croningp/NanoDiscovery/Theory/PyDScat-GPU/Examples/Core_shell/exp6/atomList_TruncatedOctahedron10.png

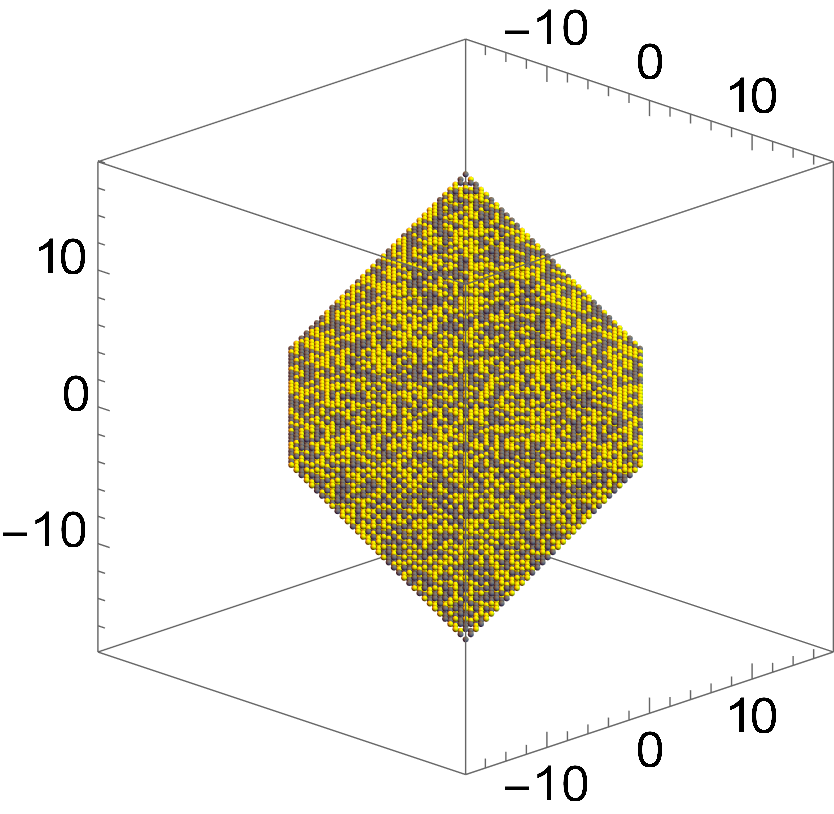
Theory/PyDScat-GPU/Examples/Core_shell/exp6/atomList_TruncatedOctahedron10.png
