croningp/NanoDiscovery/Theory/Superellipsoid/Experiment_20_20_20_1_1/Dipole.png

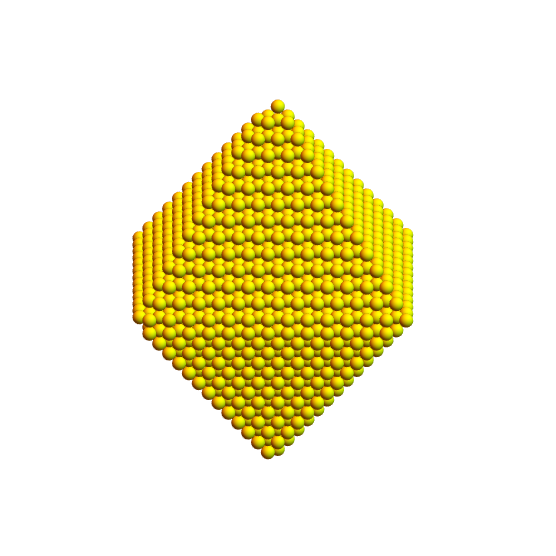
Theory/Superellipsoid/Experiment_20_20_20_1_1/Dipole.png
