croningp/NanoDiscovery/Theory/PyDScat-GPU/Examples/Core_shell/atomList_Octahedron.csv

Ag | 0. | 0. | 34.
Au | 0. | 0.5 | 33.5
Ag | 0. | 1. | 33.
Au | 0. | 1.5 | 32.5
Ag | 0. | 2. | 32.
Au | 0. | 2.5 | 31.5
Ag | 0. | 3. | 31.
Ag | 0. | 3.5 | 30.5
Au | 0. | 4. | 30.
Ag | 0. | 4.5 | 29.5
Au | 0. | 5. | 29.
Ag | 0. | 5.5 | 28.5
Ag | 0. | 6. | 28.
Ag | 0. | 6.5 | 27.5
Ag | 0. | 7. | 27.
Au | 0. | 7.5 | 26.5
Ag | 0. | 8. | 26.
Ag | 0. | 8.5 | 25.5
Ag | 0. | 9. | 25.
Au | 0. | 9.5 | 24.5
Ag | 0. | 10. | 24.
Ag | 0. | 10.5 | 23.5
Au | 0. | 11. | 23.
Ag | 0. | 11.5 | 22.5
Ag | 0. | 12. | 22.
Au | 0. | 12.5 | 21.5
Au | 0. | 13. | 21.
Ag | 0. | 13.5 | 20.5
Au | 0. | 14. | 20.
Au | 0. | 14.5 | 19.5
Ag | 0. | 15. | 19.
Ag | 0. | 15.5 | 18.5
Ag | 0. | 16. | 18.
Ag | 0. | 16.5 | 17.5
Ag | 0. | 17. | 17.
Au | 0. | 17.5 | 16.5
Ag | 0. | 18. | 16.
Ag | 0. | 18.5 | 15.5
Ag | 0. | 19. | 15.
Ag | 0. | 19.5 | 14.5
Au | 0. | 20. | 14.
Ag | 0. | 20.5 | 13.5
Ag | 0. | 21. | 13.
Au | 0. | 21.5 | 12.5
Ag | 0. | 22. | 12.
Ag | 0. | 22.5 | 11.5
Au | 0. | 23. | 11.
Au | 0. | 23.5 | 10.5
Au | 0. | 24. | 10.
Au | 0. | 24.5 | 9.5
Ag | 0. | 25. | 9.
Au | 0. | 25.5 | 8.5
Au | 0. | 26. | 8.
Au | 0. | 26.5 | 7.5
Au | 0. | 27. | 7.
Au | 0. | 27.5 | 6.5
Au | 0. | 28. | 6.
Au | 0. | 28.5 | 5.5
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
