croningp/NanoDiscovery/Theory/PyDScat-GPU/Examples/Heter_samples/exp7_custom/custom_ratio.csv

8.000000000000000444e-01 | 8.000000000000000444e-01 | 8.000000000000000444e-01 | 8.000000000000000444e-01 | 8.000000000000000444e-01 | 8.000000000000000444e-01 | 8.000000000000000444e-01 | 8.000000000000000444e-01 | 8.000000000000000444e-01 | 8.000000000000000444e-01 | 8.000000000000000444e-01 | 8.000000000000000444e-01 | 8.000000000000000444e-01 | 8.000000000000000444e-01 | 8.000000000000000444e-01 | 8.000000000000000444e-01 | 8.000000000000000444e-01 | 8.000000000000000444e-01 | 8.000000000000000444e-01 | 8.000000000000000444e-01 | 8.000000000000000444e-01 | 8.000000000000000444e-01 | 8.000000000000000444e-01 | 8.000000000000000444e-01 | 8.000000000000000444e-01 | 8.000000000000000444e-01 | 8.000000000000000444e-01 | 8.000000000000000444e-01 | 8.000000000000000444e-01 | 8.000000000000000444e-01 | 8.000000000000000444e-01 | 8.000000000000000444e-01 | 8.000000000000000444e-01 | 8.000000000000000444e-01 | 8.000000000000000444e-01 | 8.000000000000000444e-01 | 8.000000000000000444e-01 | 8.000000000000000444e-01 | 8.000000000000000444e-01 | 8.000000000000000444e-01 | 8.000000000000000444e-01 | 8.000000000000000444e-01 | 8.000000000000000444e-01 | 8.000000000000000444e-01 |
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
