croningp/NanoDiscovery/Experiments/Graph_Structure/hardware_graph.png

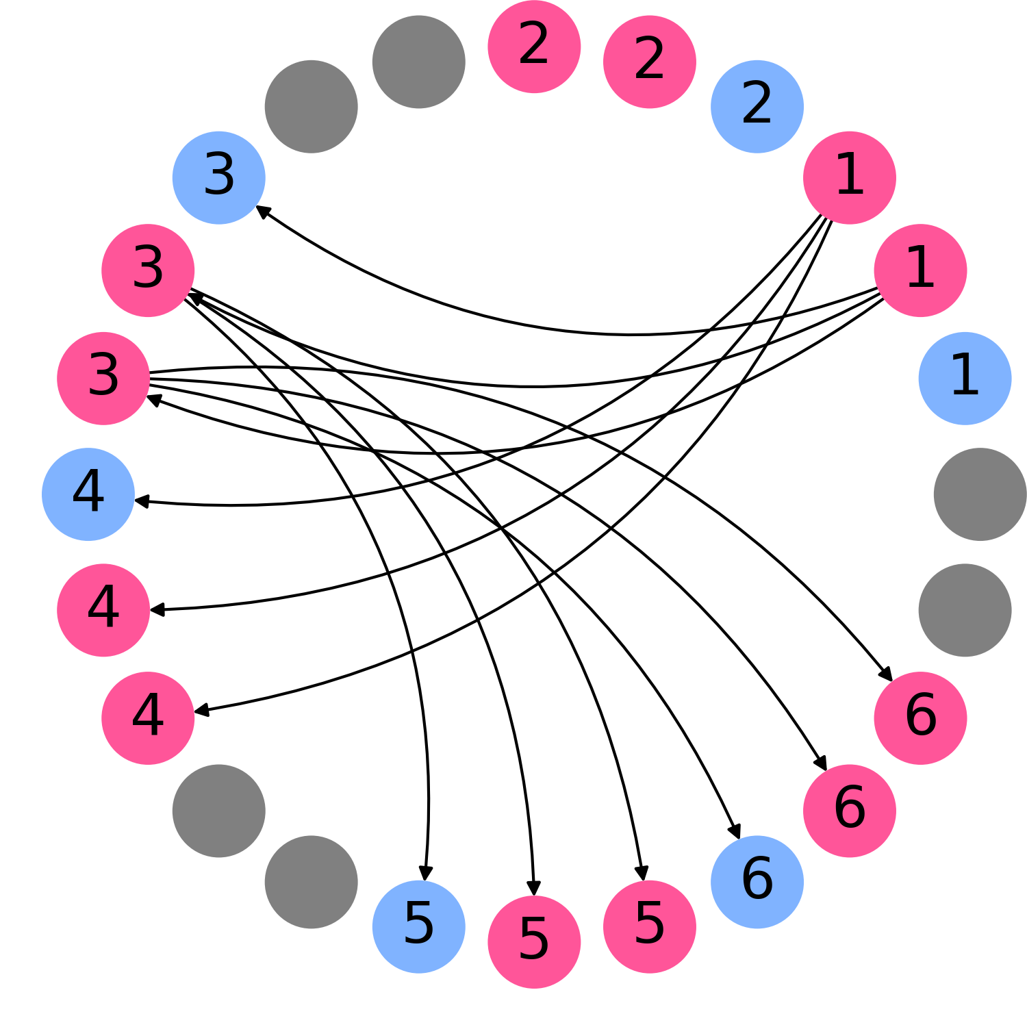
Experiments/Graph_Structure/hardware_graph.png
