croningp/NanoDiscovery/Experiments/Graph_Structure/synthesis_graph.png

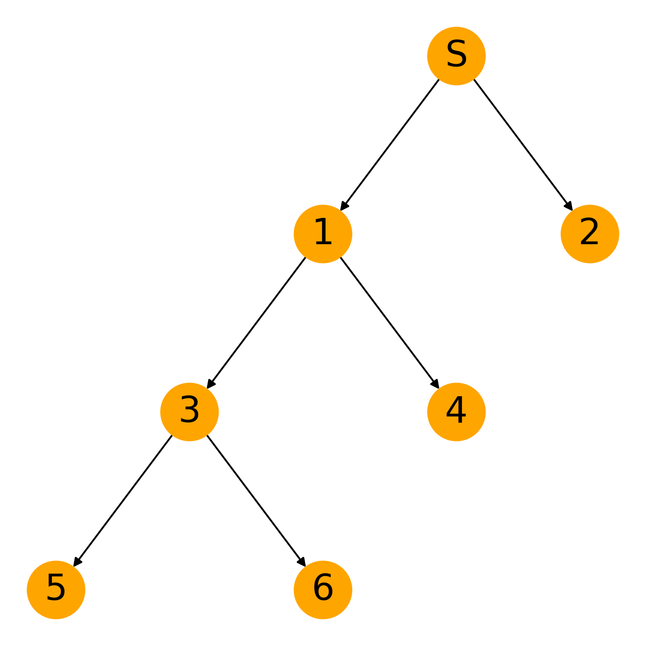
Experiments/Graph_Structure/synthesis_graph.png
