croningp/NanoDiscovery/Theory/PyDScat-GPU/Examples/Au_Ag_coreshell.png

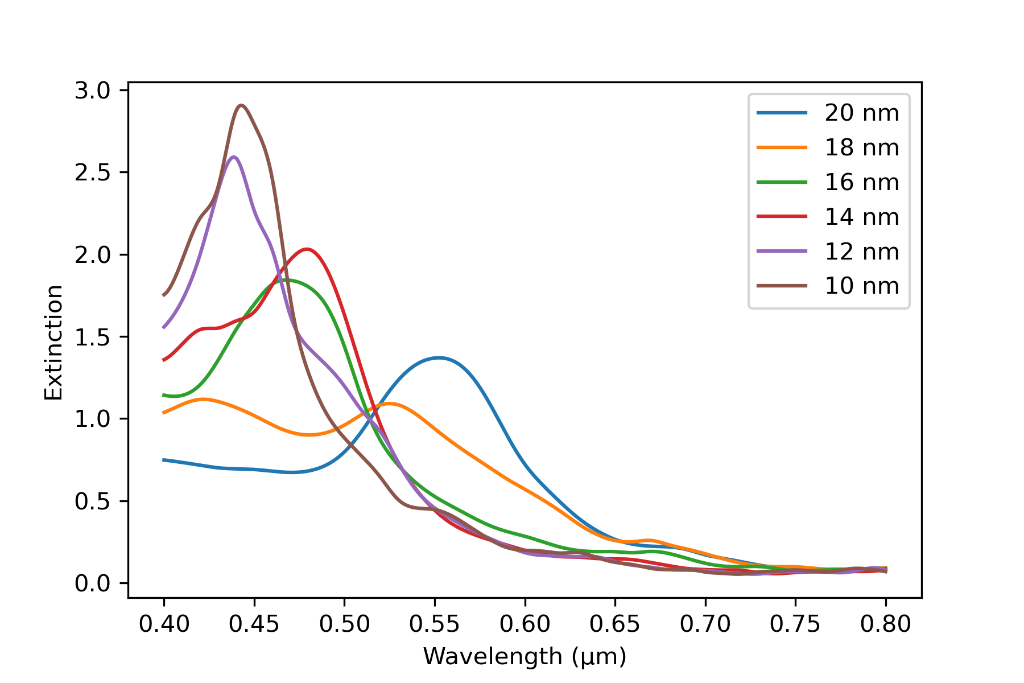
Theory/PyDScat-GPU/Examples/Au_Ag_coreshell.png
