croningp/NanoDiscovery/Theory/PyDScat-GPU/Examples/Au_Ag_homo.png

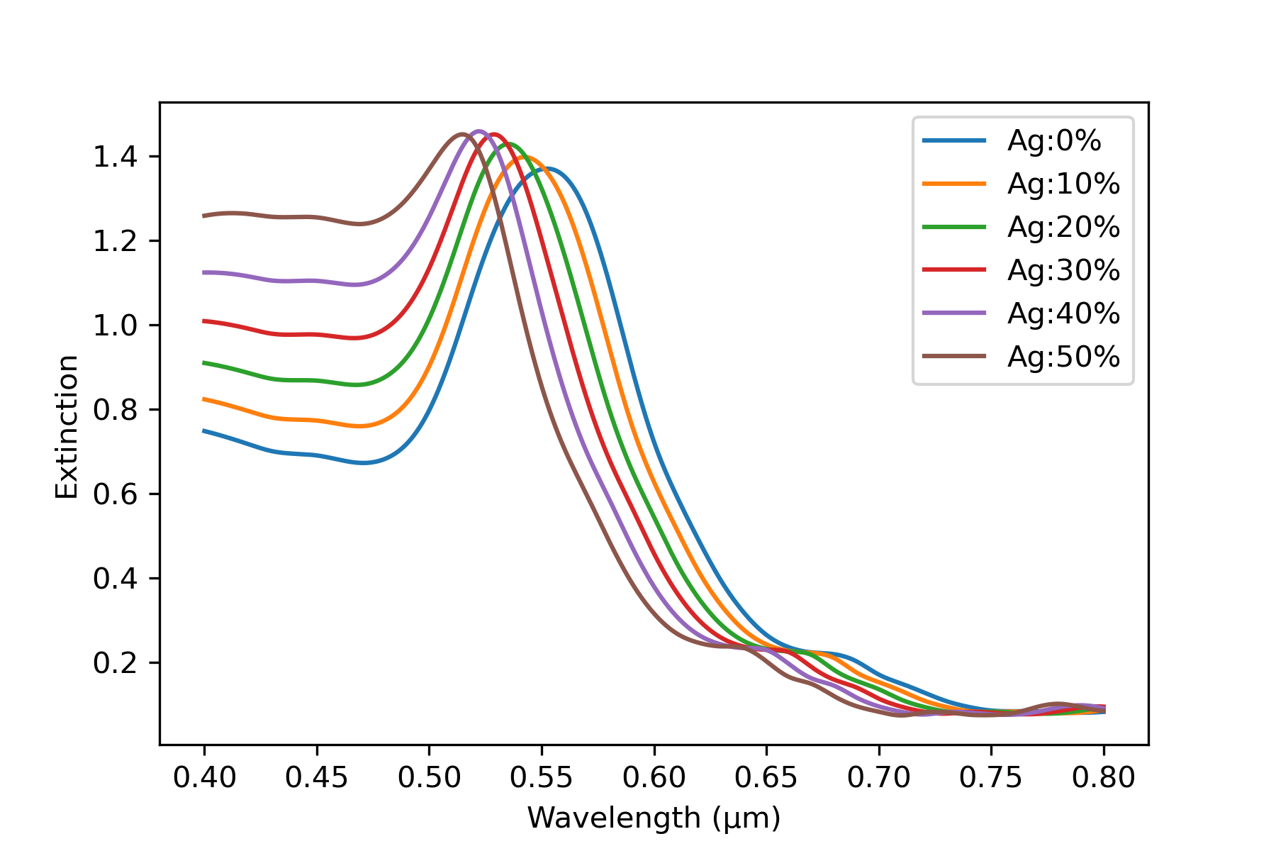
Theory/PyDScat-GPU/Examples/Au_Ag_homo.png
