croningp/NanoDiscovery/Theory/PyDScat-GPU/Examples/Core_shell/exp1/dipolePlot.png

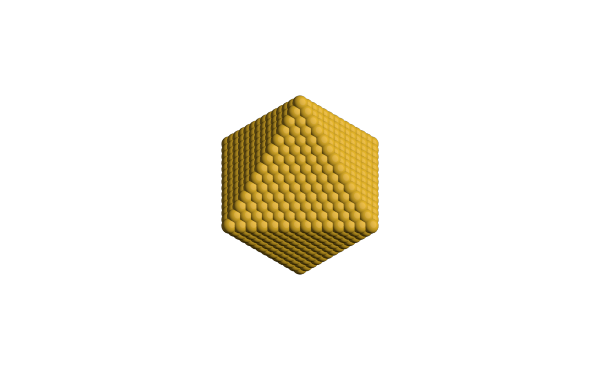
Theory/PyDScat-GPU/Examples/Core_shell/exp1/dipolePlot.png
