croningp/NanoDiscovery/Theory/PyDScat-GPU/Examples/Core_shell/exp5/atomList_TruncatedOctahedron12.png

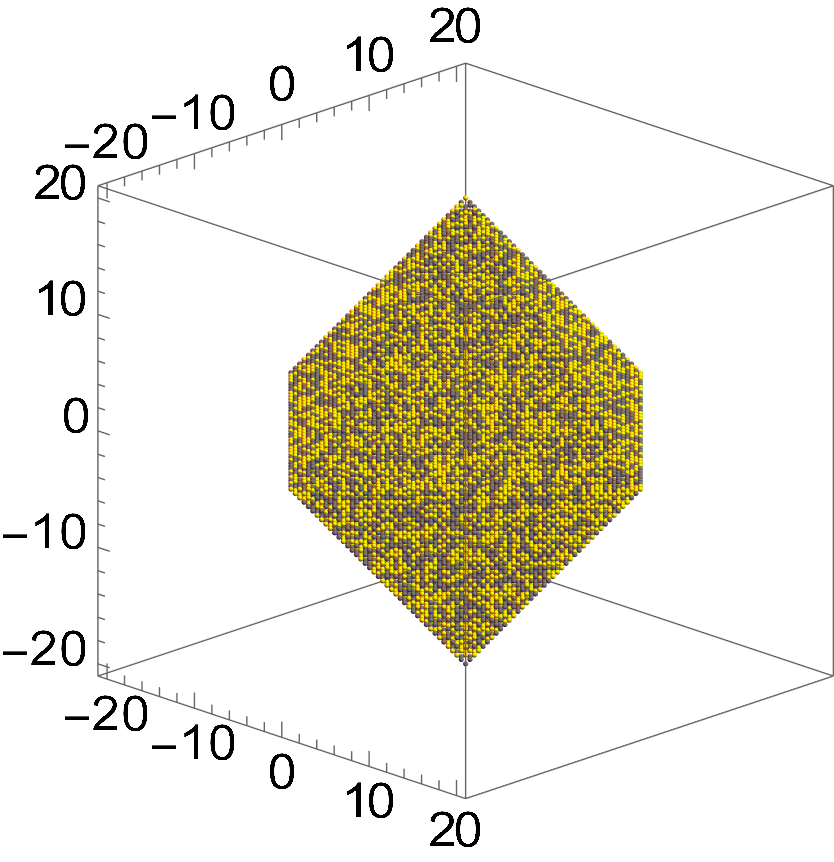
Theory/PyDScat-GPU/Examples/Core_shell/exp5/atomList_TruncatedOctahedron12.png
