croningp/NanoDiscovery/Theory/PyDScat-GPU/Examples/Core_shell/exp5/UV_Vis.png

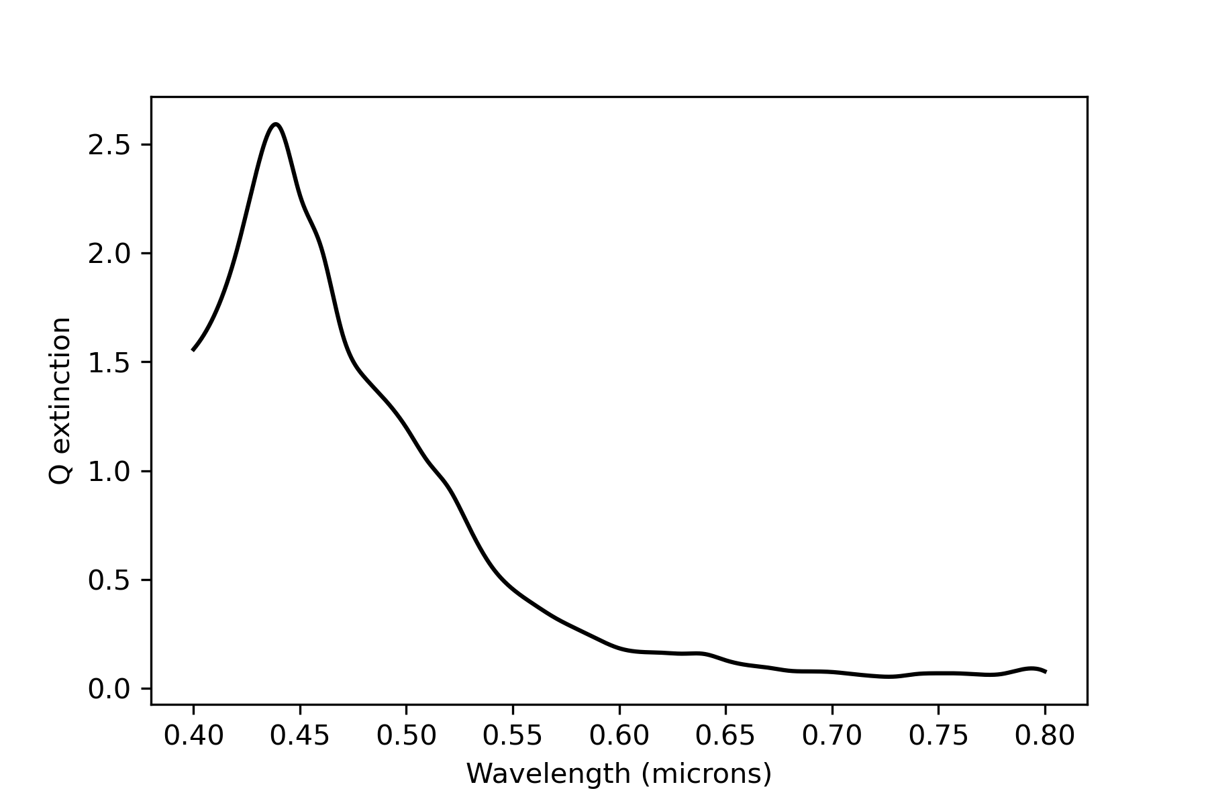
Theory/PyDScat-GPU/Examples/Core_shell/exp5/UV_Vis.png
