croningp/NanoDiscovery/Theory/PyDScat-GPU/Examples/Core_shell/exp6/UV_Vis.png

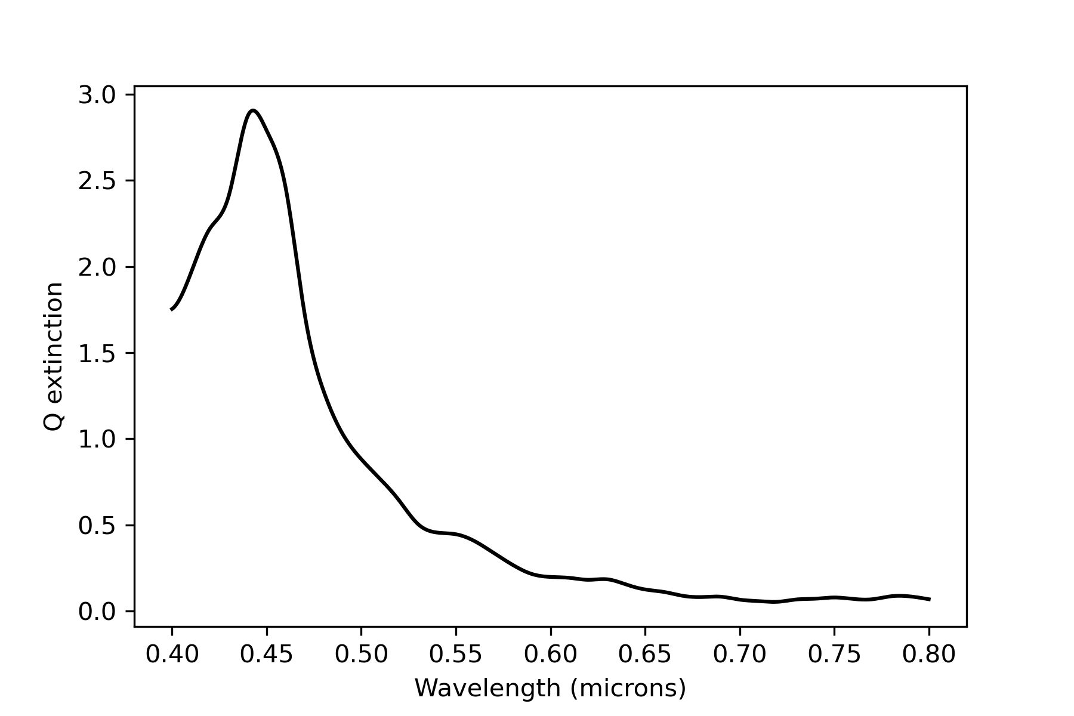
Theory/PyDScat-GPU/Examples/Core_shell/exp6/UV_Vis.png
