croningp/NanoDiscovery/Theory/PyDScat-GPU/Examples/Heter_samples/exp3/UV_Vis.png

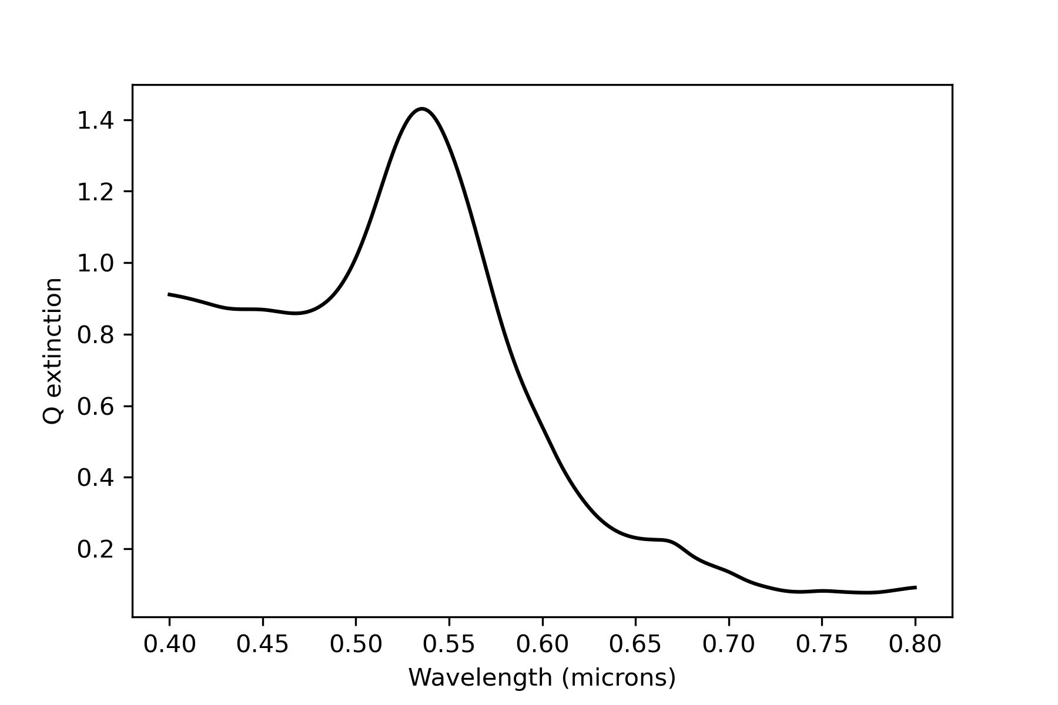
Theory/PyDScat-GPU/Examples/Heter_samples/exp3/UV_Vis.png
