croningp/NanoDiscovery/Theory/PyDScat-GPU/Examples/Heter_samples/exp5/UV_Vis.png

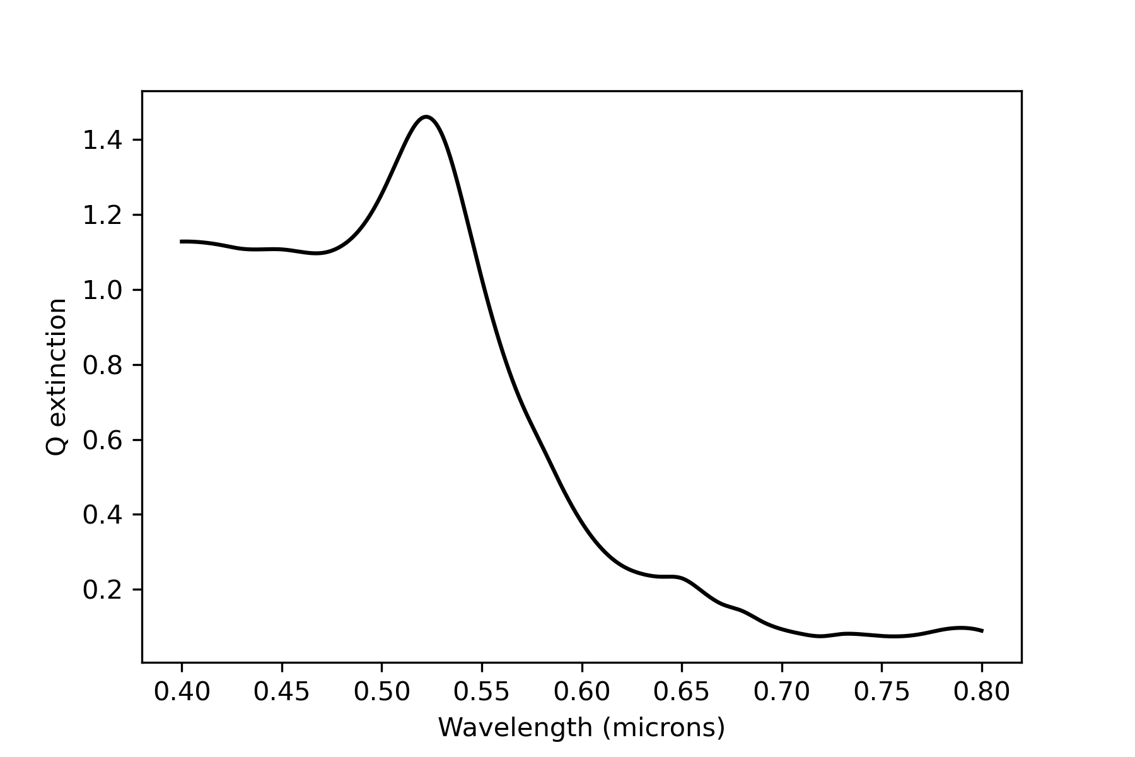
Theory/PyDScat-GPU/Examples/Heter_samples/exp5/UV_Vis.png
