croningp/NanoDiscovery/Experiments/Hardware/Spectroscopic suite/Cuts/Flow cell balcony base plate.dxf

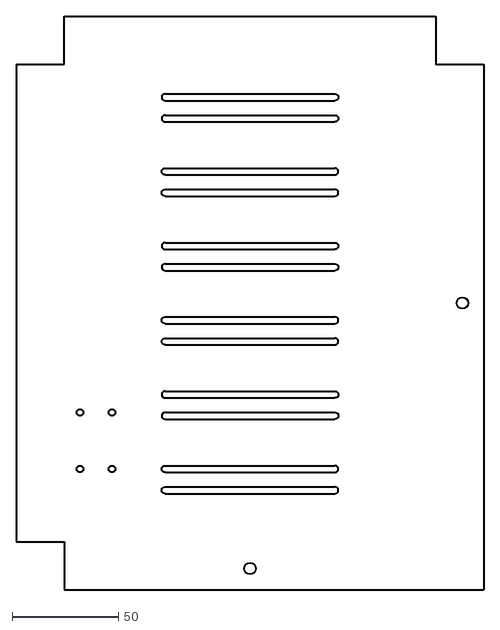
[picture p36: CAD file, 2022-08-24]
Experiments/Hardware/Spectroscopic suite/Cuts/Flow cell balcony base plate.dxf
220.0 x 270.0
