croningp/NanoDiscovery/Experiments/Hardware/Spectroscopic suite/Prints/Spectrometer shelf mount right.stl

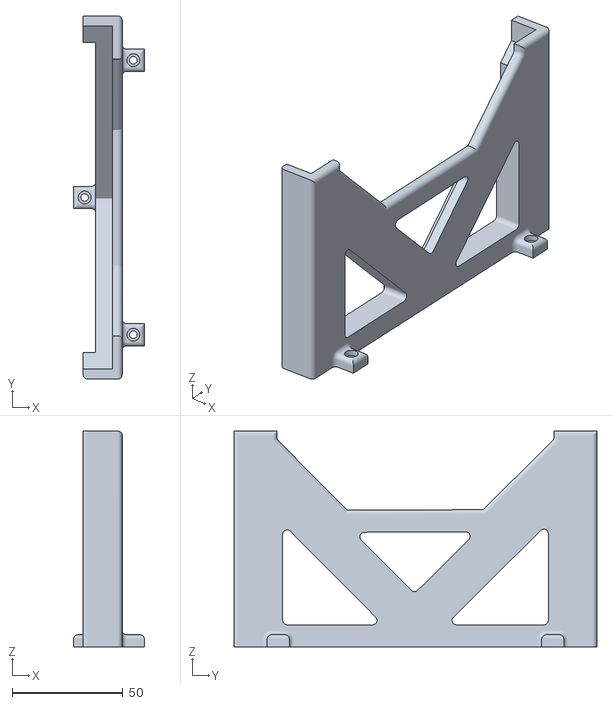
[picture p37: CAD file, 2022-08-24]
Experiments/Hardware/Spectroscopic suite/Prints/Spectrometer shelf mount right.stl
32.0 x 164.0 x 97.5
