croningp/NanoDiscovery/Experiments/Hardware/Tri-Cont shelf/Cuts/Tricont v-slot box - Base for 12 pumps 6mm.dxf

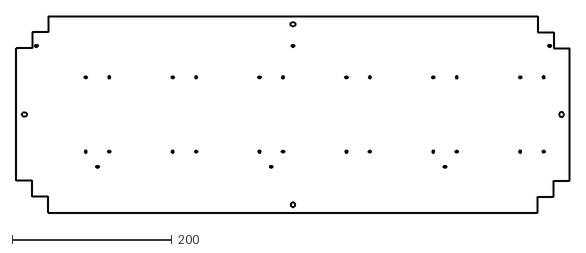
[picture p38: CAD file, 2022-08-24]
Experiments/Hardware/Tri-Cont shelf/Cuts/Tricont v-slot box - Base for 12 pumps 6mm.dxf
692.8 x 246.0
