croningp/NanoDiscovery/Experiments/Hardware/Tri-Cont shelf/Prints/Tri-cont printed stand.stl

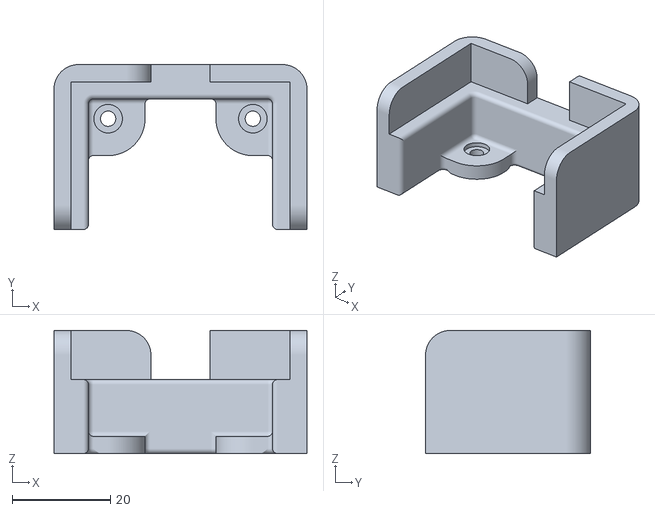
[picture p39: CAD file, 2022-08-24]
Experiments/Hardware/Tri-Cont shelf/Prints/Tri-cont printed stand.stl
51.4 x 33.5 x 25.0
