croningp/NanoDiscovery/Experiments/Software/modularwheelplatform/docs/hardware/Prints/Dispensing unit/Kinesis needles/ClusterBot/Dispensing module Kinesis needles ClusterBot Inlay.stl

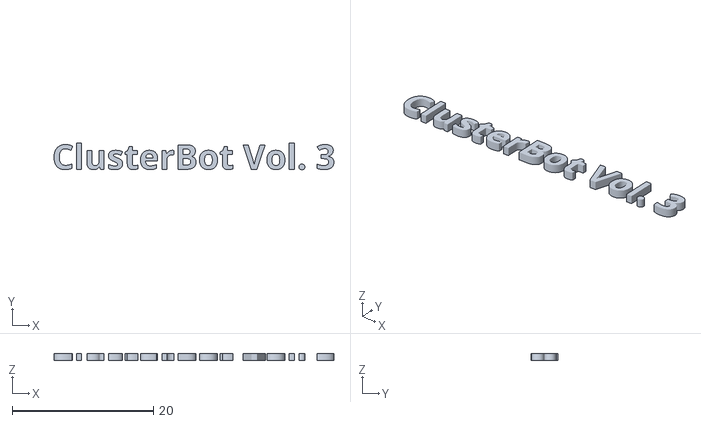
[picture p40: CAD file, 2022-08-24]
Experiments/Software/modularwheelplatform/docs/hardware/Prints/Dispensing unit/Kinesis needles/ClusterBot/Dispensing module Kinesis needles ClusterBot Inlay.stl
39.6 x 3.76 x 1.00
