croningp/NanoDiscovery/Experiments/Software/modularwheelplatform/docs/hardware/Prints/Dispensing unit/Kinesis needles/MapleBot/Dispensing module Kinesis needles MapleBot- inlay.stl

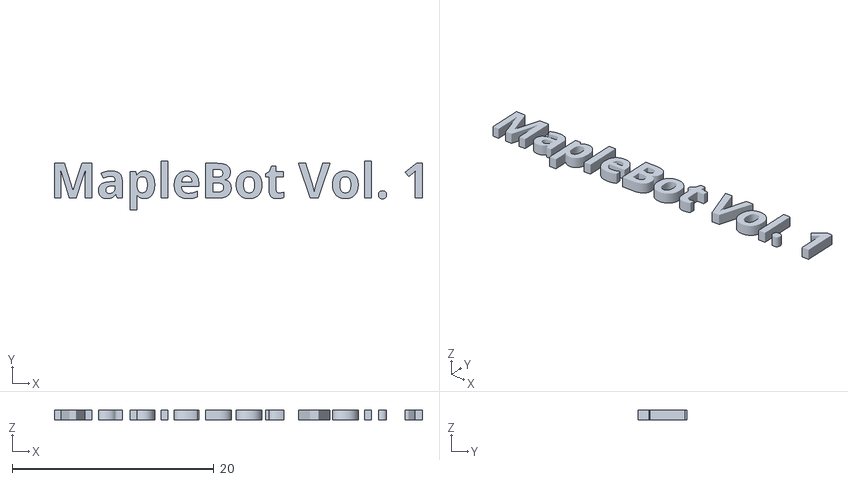
[picture p41: CAD file, 2022-08-24]
Experiments/Software/modularwheelplatform/docs/hardware/Prints/Dispensing unit/Kinesis needles/MapleBot/Dispensing module Kinesis needles MapleBot- inlay.stl
36.5 x 4.86 x 1.00
