croningp/NanoDiscovery/Experiments/Software/modularwheelplatform/docs/hardware/Prints/Dispensing unit/Kinesis needles/Modular wheel/Dispensing module 7 Kinesis needles - MW inlay.stl

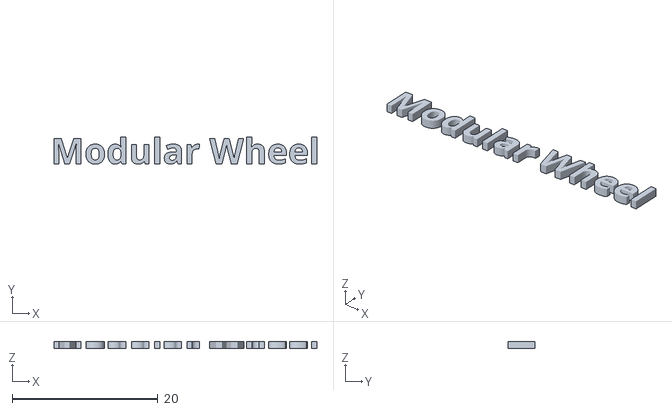
[picture p42: CAD file, 2022-08-24]
Experiments/Software/modularwheelplatform/docs/hardware/Prints/Dispensing unit/Kinesis needles/Modular wheel/Dispensing module 7 Kinesis needles - MW inlay.stl
36.1 x 3.74 x 1.00
