croningp/NanoDiscovery/Experiments/Software/modularwheelplatform/docs/hardware/Prints/Dispensing unit/Kinesis needles/NanoBot/Dispensing module Kinesis needles NanoBot Inlay.stl

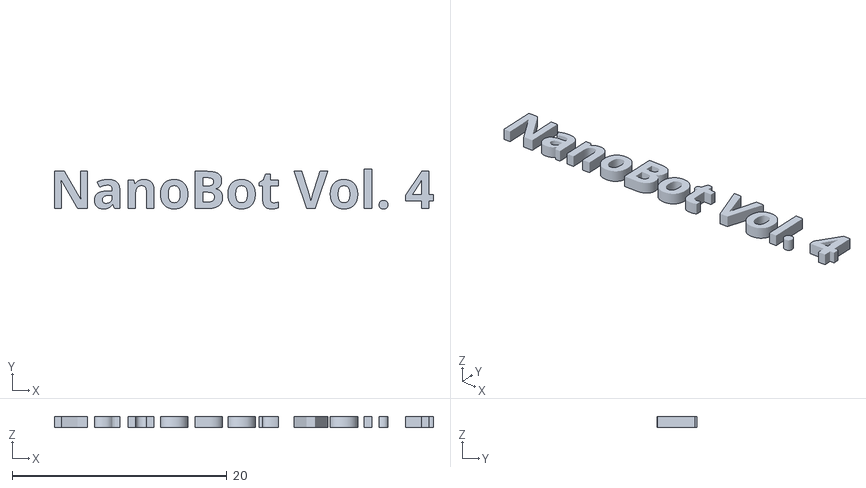
[picture p43: CAD file, 2022-08-24]
Experiments/Software/modularwheelplatform/docs/hardware/Prints/Dispensing unit/Kinesis needles/NanoBot/Dispensing module Kinesis needles NanoBot Inlay.stl
35.3 x 3.76 x 1.00
