croningp/NanoDiscovery/Experiments/Software/modularwheelplatform/docs/hardware/Prints/Dispensing unit/Raw tubes/Dispesning 7 x 1-16 raw tubes securing piece.stl

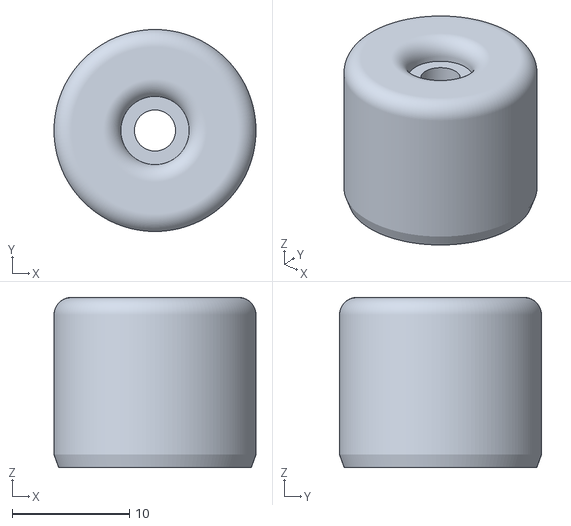
[picture p44: CAD file, 2022-08-24]
Experiments/Software/modularwheelplatform/docs/hardware/Prints/Dispensing unit/Raw tubes/Dispesning 7 x 1-16 raw tubes securing piece.stl
17.2 x 17.2 x 14.5
