croningp/NanoDiscovery/Experiments/Software/modularwheelplatform/docs/hardware/StirringRingPCB/parts/XHP-2.STEP

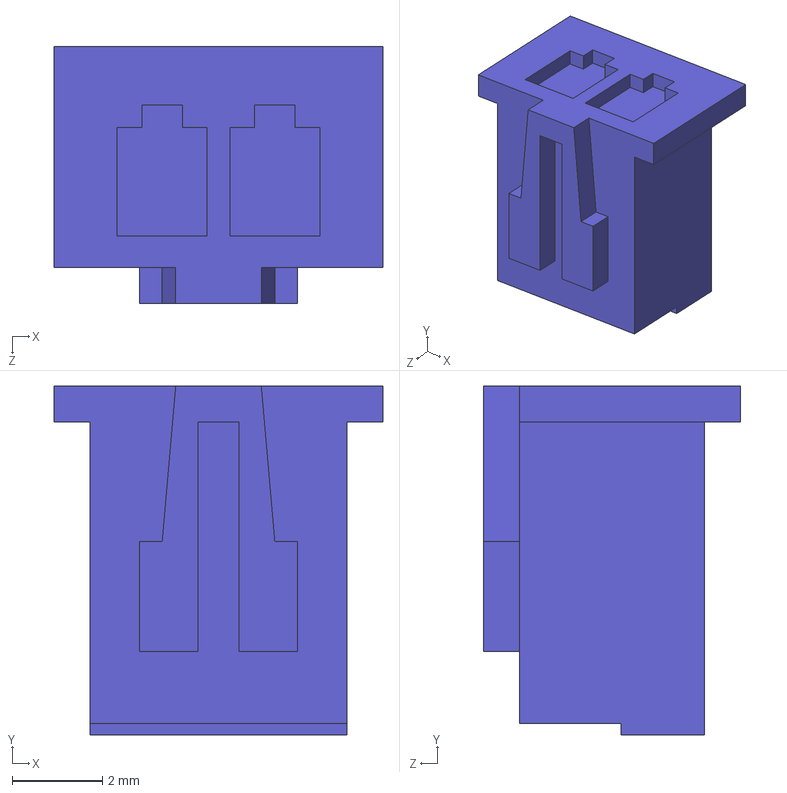
[picture p45: CAD file, 2022-08-24]
Experiments/Software/modularwheelplatform/docs/hardware/StirringRingPCB/parts/XHP-2.STEP
7.30 x 7.75 x 5.70 mm
