croningp/NanoDiscovery/Experiments/Hardware/CRM advanced modules/Cuts/Wash and storage stations/Fixed wash station 3 levels of vial holder cuts.dxf

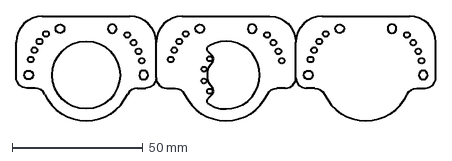
[picture p46: CAD file, 2022-08-24]
Experiments/Hardware/CRM advanced modules/Cuts/Wash and storage stations/Fixed wash station 3 levels of vial holder cuts.dxf
160.6 x 40.0 mm
