croningp/NanoDiscovery/Experiments/Hardware/CRM advanced modules/Prints/pH module/Horizontal MSD motor to v-bar mount cap- Nema 11.stl

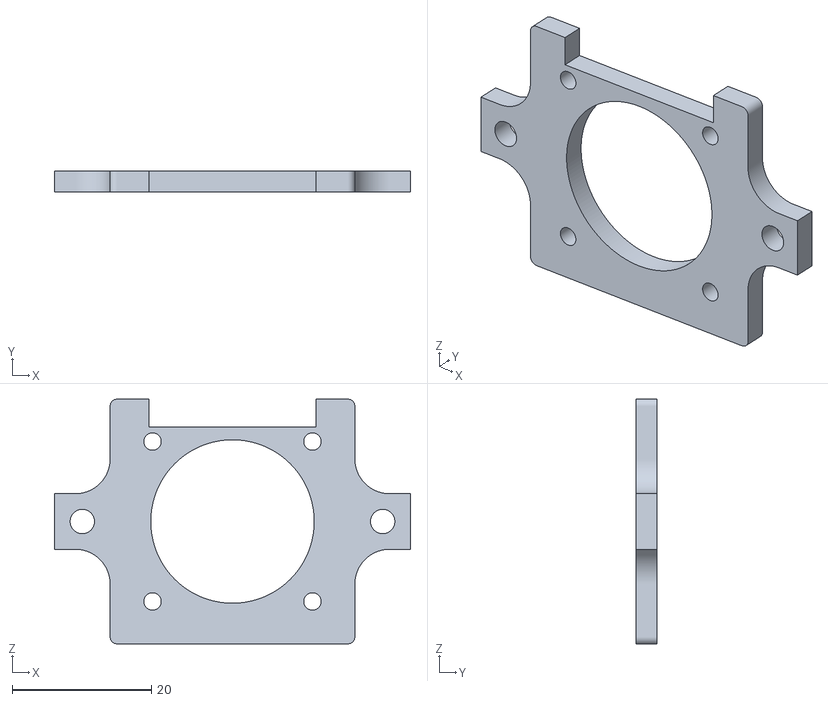
[picture p47: CAD file, 2022-08-24]
Experiments/Hardware/CRM advanced modules/Prints/pH module/Horizontal MSD motor to v-bar mount cap- Nema 11.stl
51.2 x 3.00 x 35.2
