croningp/NanoDiscovery/Experiments/Hardware/CRM advanced modules/Prints/Sample extraction analysis/V-slot bound base motor + rail mount.stl

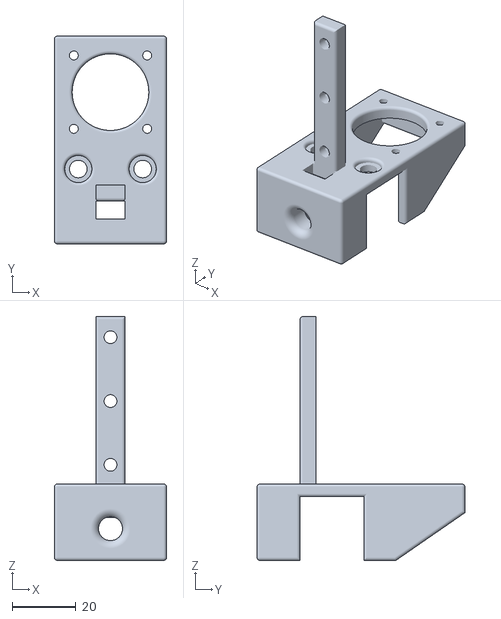
[picture p48: CAD file, 2022-08-24]
Experiments/Hardware/CRM advanced modules/Prints/Sample extraction analysis/V-slot bound base motor + rail mount.stl
35.2 x 65.2 x 76.5
