croningp/NanoDiscovery/Experiments/Hardware/Modular wheel/Cuts/Base plate and fan stirring ring 6mm.dxf

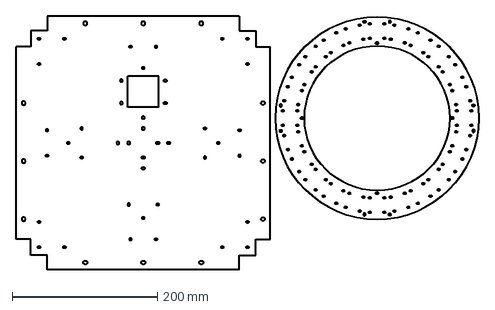
[picture p49: CAD file, 2022-08-24]
Experiments/Hardware/Modular wheel/Cuts/Base plate and fan stirring ring 6mm.dxf
637.5 x 350.0 mm
