croningp/NanoDiscovery/Experiments/Hardware/Modular wheel/Prints/Base plate parts/Leveling arc - 58.75.stl

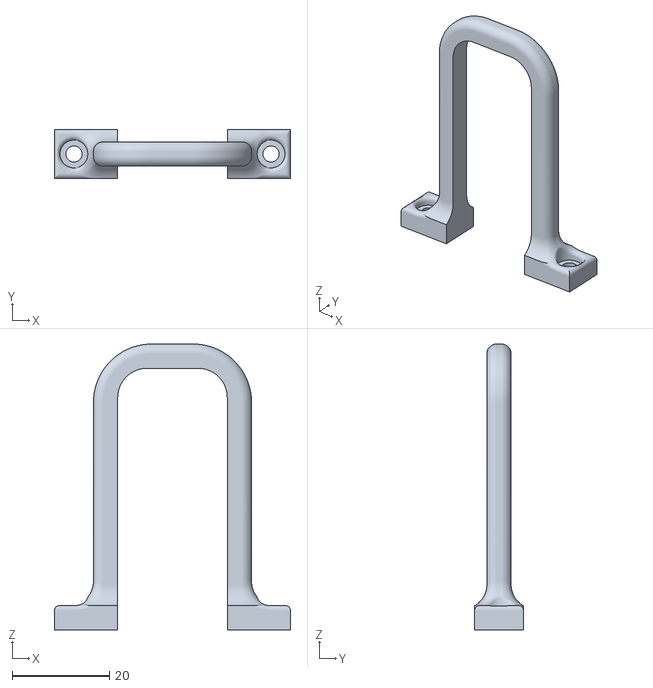
[picture p50: CAD file, 2022-08-24]
Experiments/Hardware/Modular wheel/Prints/Base plate parts/Leveling arc - 58.75.stl
48.5 x 10.0 x 58.8
