croningp/NanoDiscovery/Experiments/Hardware/Modular wheel/Prints/Stirring magnet housing/Magnet housing base.stl

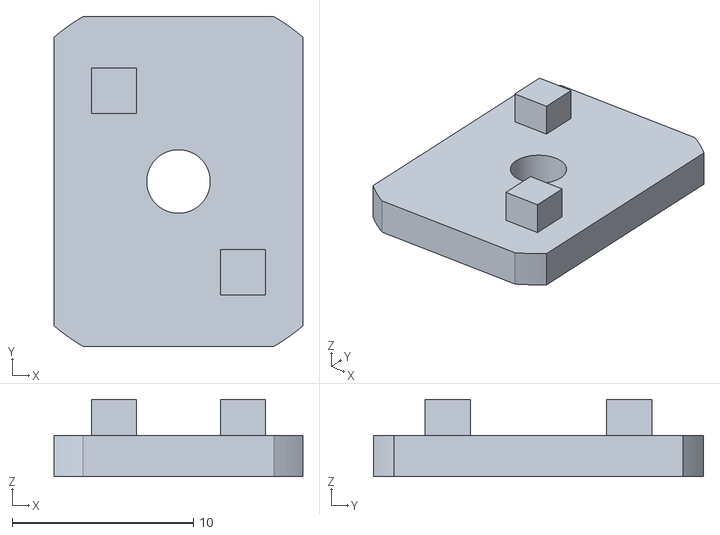
[picture p51: CAD file, 2022-08-24]
Experiments/Hardware/Modular wheel/Prints/Stirring magnet housing/Magnet housing base.stl
13.7 x 18.2 x 4.25
