croningp/NanoDiscovery/Experiments/Hardware/Platform box/Cuts/Box base parts - Back left.dxf

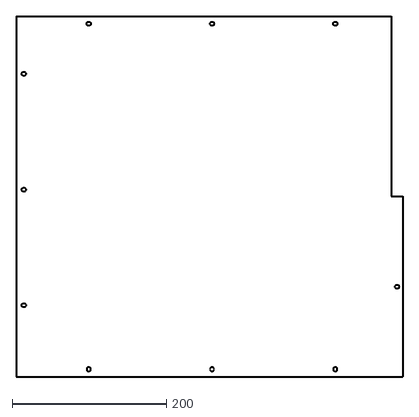
[picture p52: CAD file, 2022-08-24]
Experiments/Hardware/Platform box/Cuts/Box base parts - Back left.dxf
501.5 x 468.0
