croningp/NanoDiscovery/Experiments/Hardware/Quality of life/Stock bottle tube holders/Stock solution tube holder- Inlay.stl

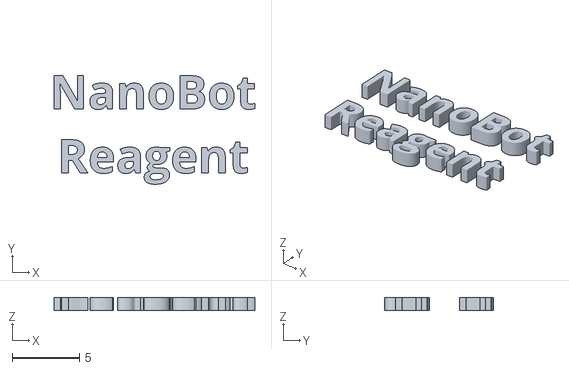
[picture p53: CAD file, 2022-08-24]
Experiments/Hardware/Quality of life/Stock bottle tube holders/Stock solution tube holder- Inlay.stl
14.9 x 8.06 x 1.00
