croningp/NanoDiscovery/Experiments/Hardware/Spectroscopic suite/Cuts/Spectrometer acrylic shelf.dxf

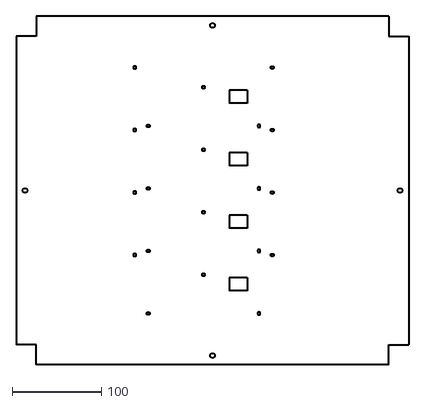
[picture p54: CAD file, 2022-08-24]
Experiments/Hardware/Spectroscopic suite/Cuts/Spectrometer acrylic shelf.dxf
440.0 x 390.0
