croningp/NanoDiscovery/Experiments/Hardware/Tri-Cont shelf/Cuts/Tricont v-slot box - Tricont guide outline 12 pumps 4mm.dxf

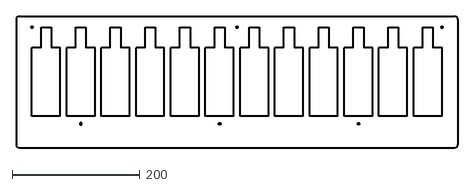
[picture p56: CAD file, 2022-08-24]
Experiments/Hardware/Tri-Cont shelf/Cuts/Tricont v-slot box - Tricont guide outline 12 pumps 4mm.dxf
692.8 x 206.0
