croningp/NanoDiscovery/Experiments/Hardware/Tri-Cont shelf/Prints/v-slot mounted tube guide.stl

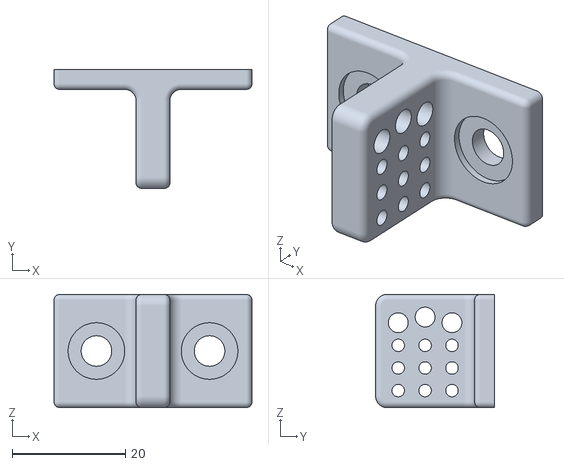
[picture p57: CAD file, 2022-08-24]
Experiments/Hardware/Tri-Cont shelf/Prints/v-slot mounted tube guide.stl
35.0 x 21.0 x 20.0
