croningp/NanoDiscovery/Experiments/Software/modularwheelplatform/docs/hardware/StirringRingPCB/parts/ring.sldprt

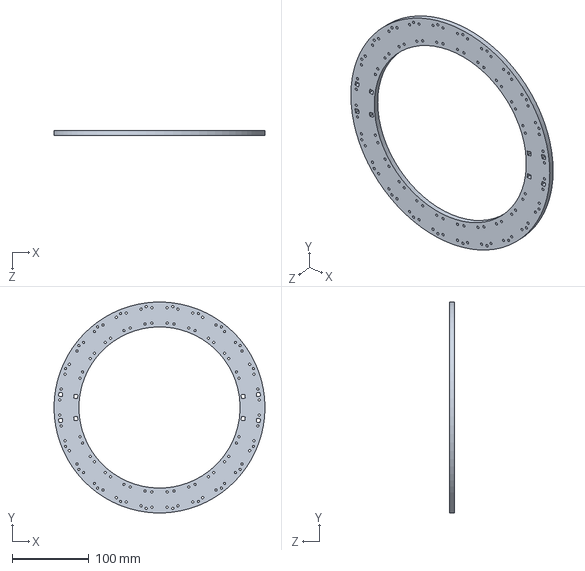
[picture p58: CAD file, 2022-08-24]
Experiments/Software/modularwheelplatform/docs/hardware/StirringRingPCB/parts/ring.sldprt
275.0 x 274.8 x 6.00 mm
