croningp/NanoDiscovery/Experiments/Hardware/CRM advanced modules/Prints/pH module/MSD- Long reach probe mount - Probe holder- securing piece.stl

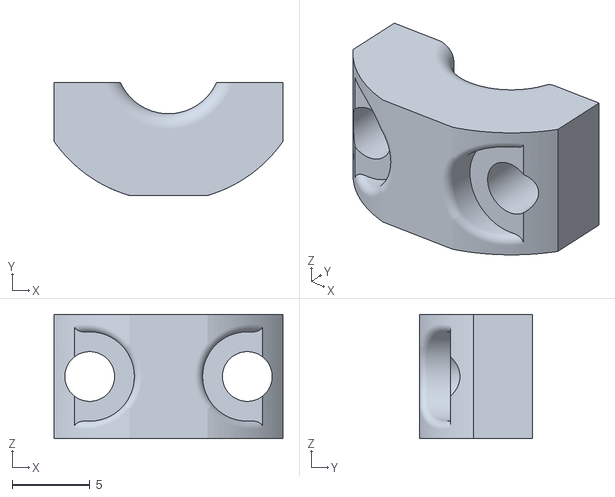
[picture p59: CAD file, 2022-08-24]
Experiments/Hardware/CRM advanced modules/Prints/pH module/MSD- Long reach probe mount - Probe holder- securing piece.stl
14.8 x 7.28 x 8.00
