croningp/NanoDiscovery/Experiments/Hardware/CRM advanced modules/Prints/Sample extraction storage/Wash station- Fixed, acrylic mounted base.stl

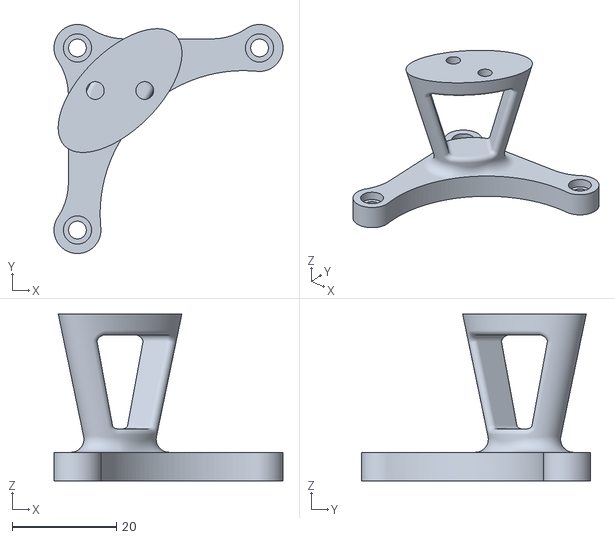
[picture p60: CAD file, 2022-08-24]
Experiments/Hardware/CRM advanced modules/Prints/Sample extraction storage/Wash station- Fixed, acrylic mounted base.stl
43.9 x 43.9 x 32.0
