croningp/NanoDiscovery/Experiments/Hardware/Platform box/Cuts/Box base parts - Right wall.dxf

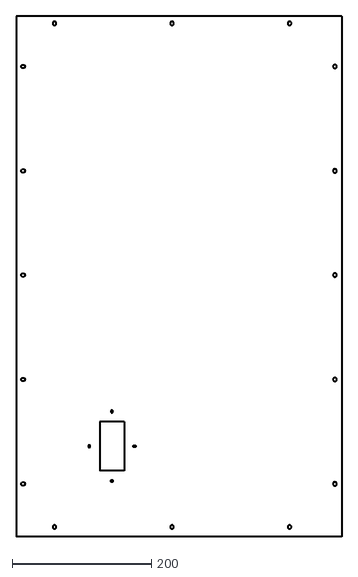
[picture p61: CAD file, 2022-08-24]
Experiments/Hardware/Platform box/Cuts/Box base parts - Right wall.dxf
468.0 x 748.0
