croningp/NanoDiscovery/Experiments/Hardware/Quality of life/Stock bottle tube holders/Stock solution tube holder - Slider.stl

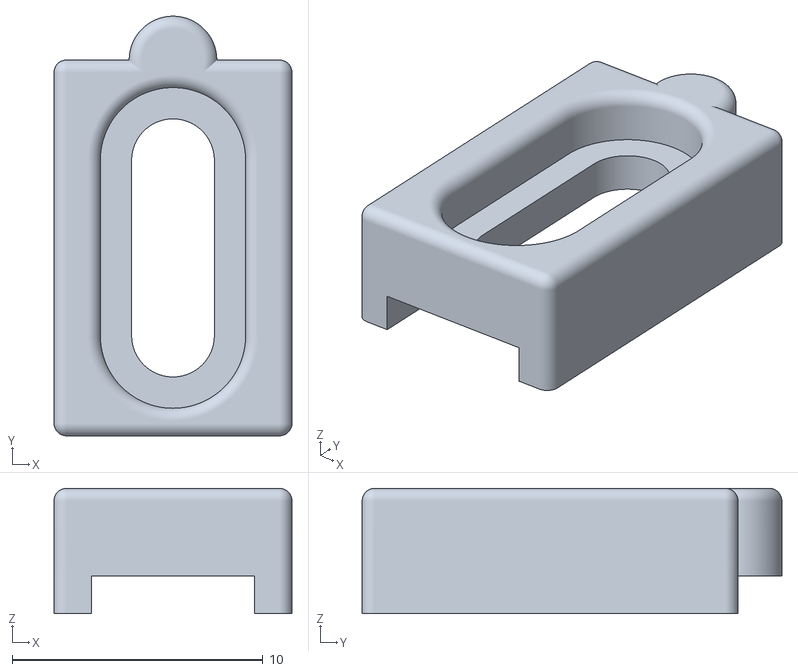
[picture p62: CAD file, 2022-08-24]
Experiments/Hardware/Quality of life/Stock bottle tube holders/Stock solution tube holder - Slider.stl
9.50 x 16.8 x 5.00
