croningp/NanoDiscovery/Experiments/Hardware/Spectroscopic suite/Prints/Corner unit flow cell mounts.stl

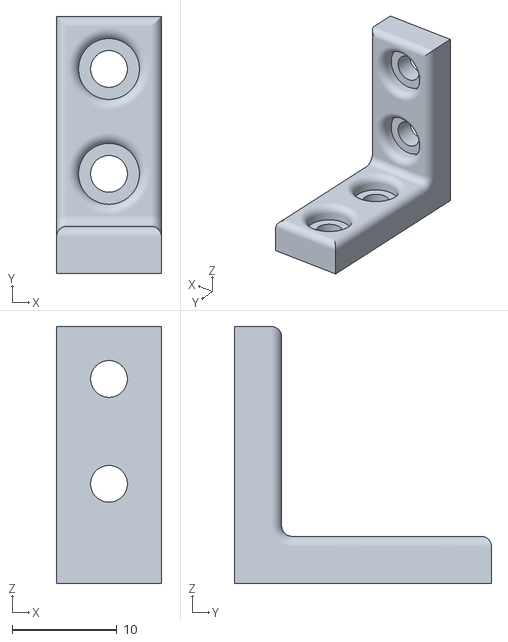
[picture p63: CAD file, 2022-08-24]
Experiments/Hardware/Spectroscopic suite/Prints/Corner unit flow cell mounts.stl
10.0 x 24.5 x 24.5
