croningp/NanoDiscovery/Experiments/Software/modularwheelplatform/docs/hardware/Prints/Stirring ring/PCB mounting block.stl

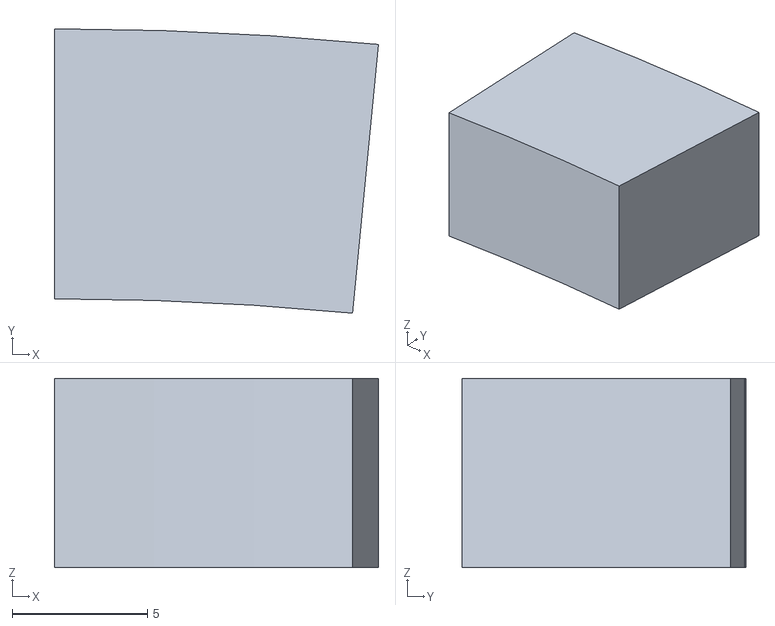
[picture p64: CAD file, 2022-08-24]
Experiments/Software/modularwheelplatform/docs/hardware/Prints/Stirring ring/PCB mounting block.stl
12.0 x 10.5 x 7.00
