croningp/NanoDiscovery/Experiments/Software/modularwheelplatform/docs/hardware/StirringRingPCB/parts/plate.sldprt

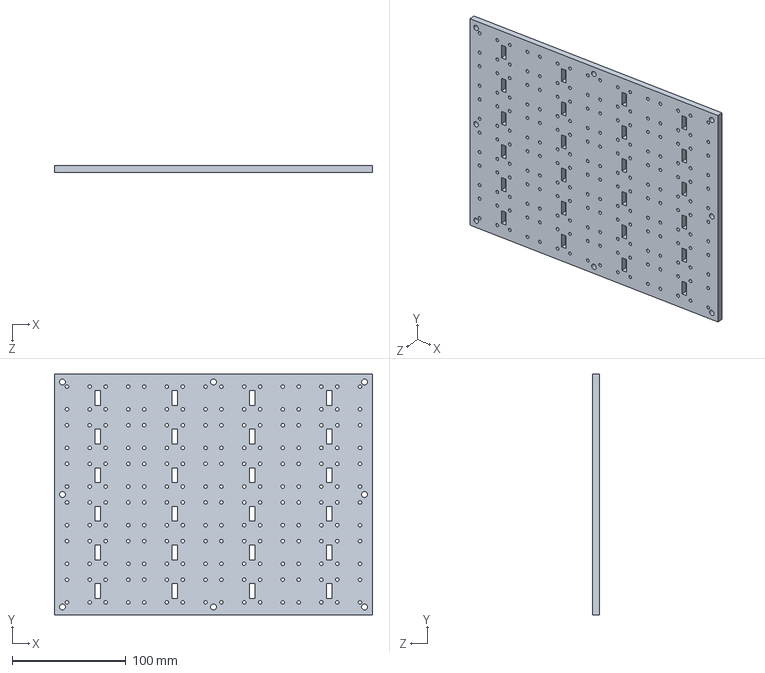
[picture p65: CAD file, 2022-08-24]
Experiments/Software/modularwheelplatform/docs/hardware/StirringRingPCB/parts/plate.sldprt
280.0 x 212.0 x 6.00 mm
