croningp/NanoDiscovery/Experiments/Hardware/Platform box/Cuts/Box base parts - Base middle.dxf

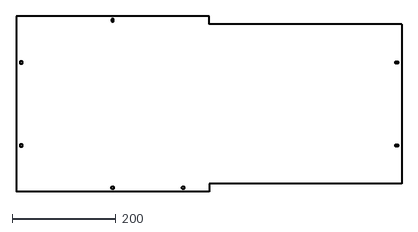
[picture p66: CAD file, 2022-08-24]
Experiments/Hardware/Platform box/Cuts/Box base parts - Base middle.dxf
744.0 x 337.8
