croningp/NanoDiscovery/Experiments/Hardware/CRM advanced modules/Prints/Sample extraction storage/Horizontal MSD motor to v-bar mount- Nema 11.stl

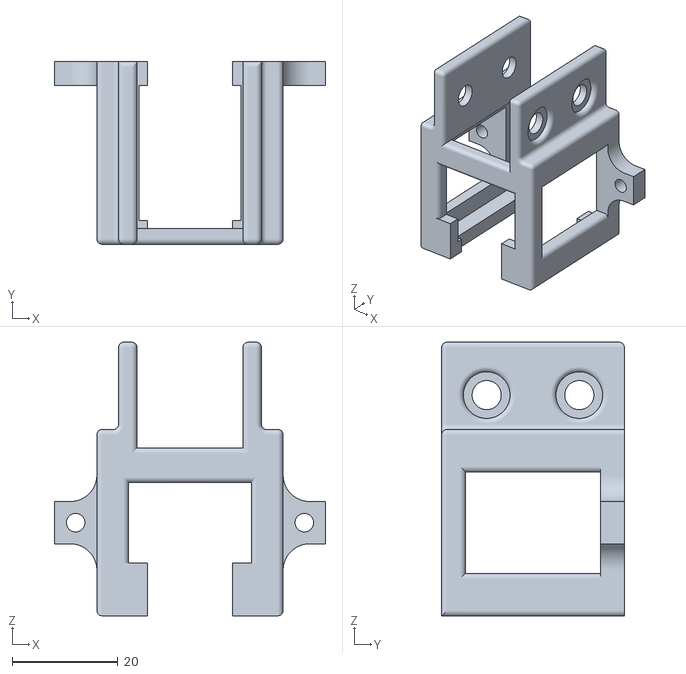
[picture p67: CAD file, 2022-08-24]
Experiments/Hardware/CRM advanced modules/Prints/Sample extraction storage/Horizontal MSD motor to v-bar mount- Nema 11.stl
51.2 x 34.5 x 51.7
