croningp/NanoDiscovery/Experiments/Hardware/Platform box/Cuts/Interior stock shelf - NB- Stock solution shelf base.dxf

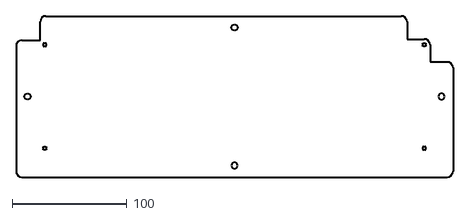
[picture p68: CAD file, 2022-08-24]
Experiments/Hardware/Platform box/Cuts/Interior stock shelf - NB- Stock solution shelf base.dxf
380.0 x 140.0
