croningp/NanoDiscovery/Experiments/Software/modularwheelplatform/docs/hardware/StirringRingPCB/parts/S2B-XH-A.STEP

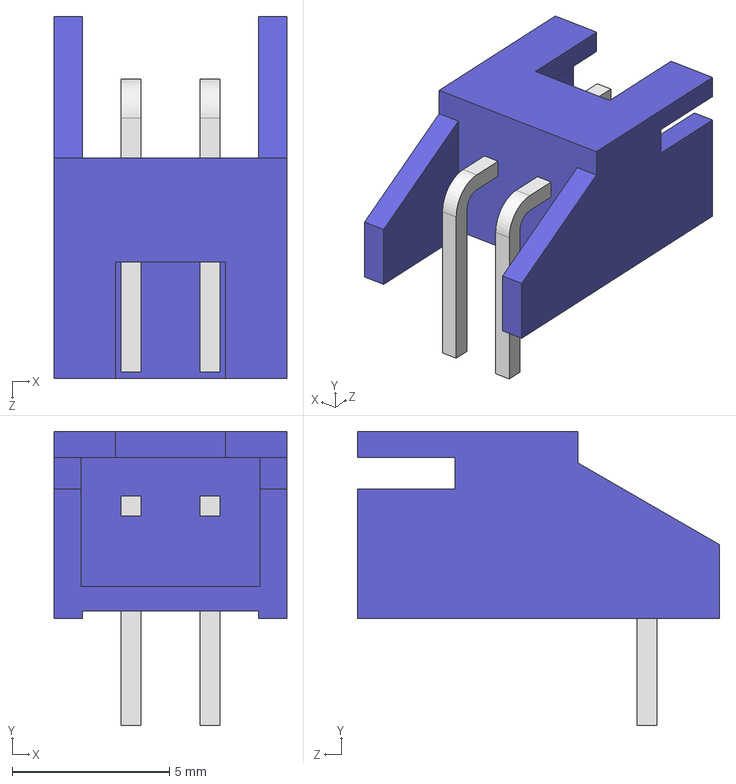
[picture p69: CAD file, 2022-08-24]
Experiments/Software/modularwheelplatform/docs/hardware/StirringRingPCB/parts/S2B-XH-A.STEP
7.40 x 9.35 x 11.5 mm
