croningp/NanoDiscovery/Experiments/Hardware/CRM advanced modules/Prints/pH module/MSD- Long reach probe mount - Probe tube holder- 2.stl

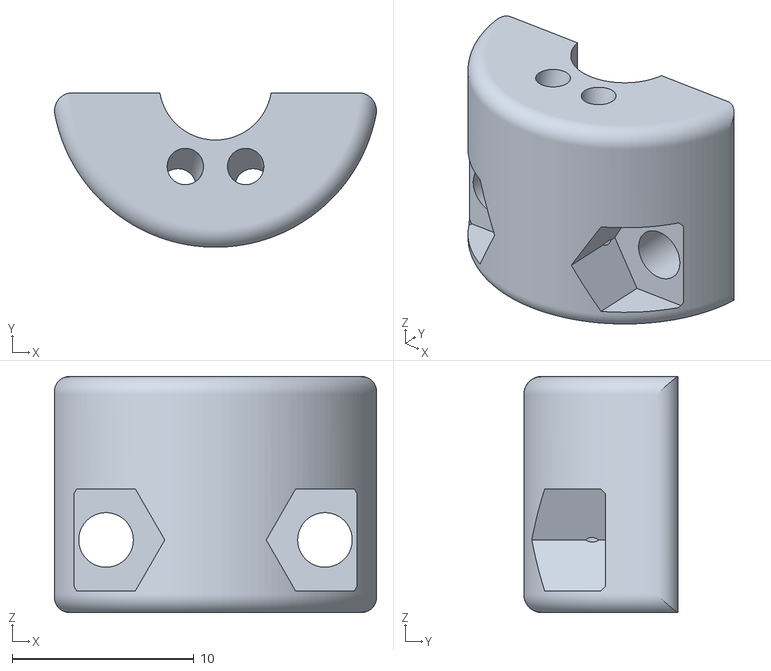
[picture p70: CAD file, 2022-08-24]
Experiments/Hardware/CRM advanced modules/Prints/pH module/MSD- Long reach probe mount - Probe tube holder- 2.stl
17.7 x 8.50 x 13.0
