croningp/NanoDiscovery/Experiments/Hardware/Platform box/Cuts/Box base parts - Back right.dxf

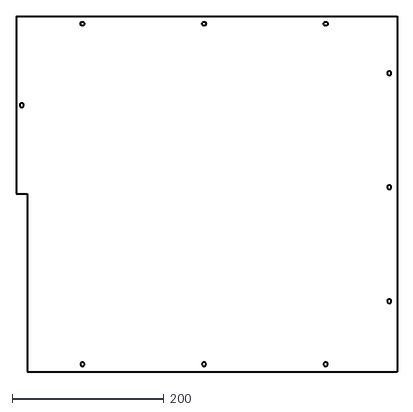
[picture p71: CAD file, 2022-08-24]
Experiments/Hardware/Platform box/Cuts/Box base parts - Back right.dxf
501.5 x 468.0
