croningp/NanoDiscovery/Experiments/Hardware/CRM advanced modules/Prints/Sample extraction storage/Horizontal MSD movement v-slot mount.stl

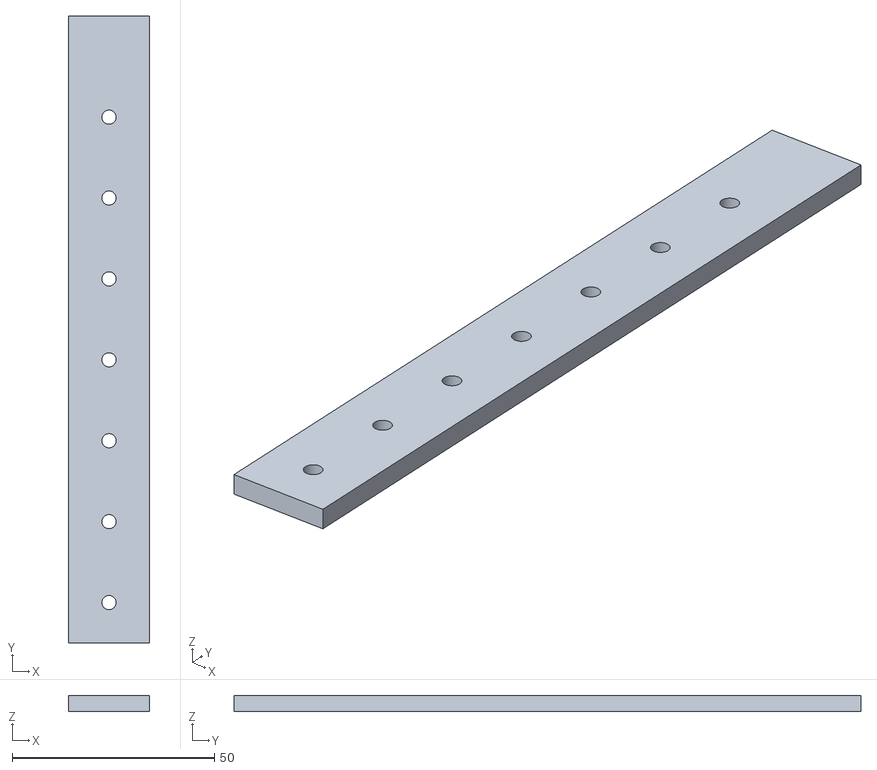
[picture p72: CAD file, 2022-08-24]
Experiments/Hardware/CRM advanced modules/Prints/Sample extraction storage/Horizontal MSD movement v-slot mount.stl
20.0 x 155.0 x 4.00
