croningp/NanoDiscovery/Experiments/Hardware/Platform box/Cuts/Interior stock shelf - NB- Stock shelf top.dxf

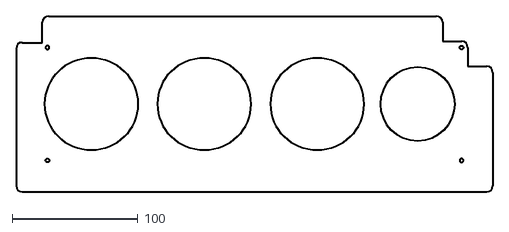
[picture p73: CAD file, 2022-08-24]
Experiments/Hardware/Platform box/Cuts/Interior stock shelf - NB- Stock shelf top.dxf
380.0 x 140.0
