croningp/NanoDiscovery/Experiments/Hardware/Platform box/Cuts/Box base parts - Top right.dxf

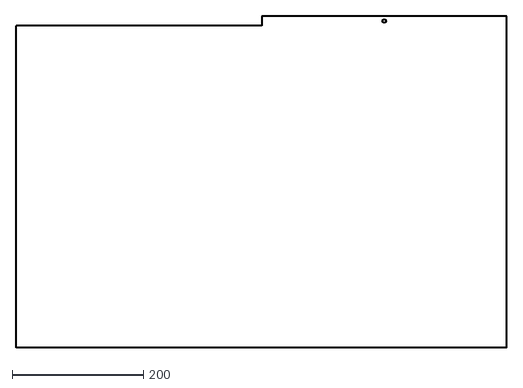
[picture p74: CAD file, 2022-08-24]
Experiments/Hardware/Platform box/Cuts/Box base parts - Top right.dxf
748.0 x 505.5
