croningp/NanoDiscovery/Experiments/Hardware/Platform box/Cuts/Box base parts - Base left.dxf

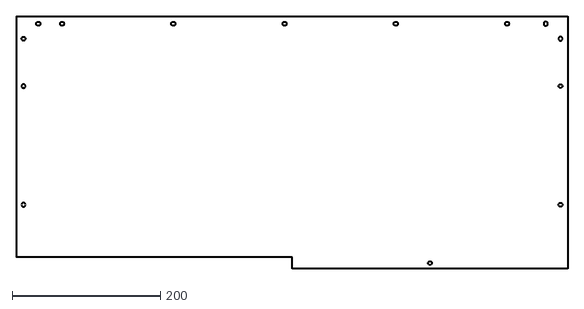
[picture p75: CAD file, 2022-08-24]
Experiments/Hardware/Platform box/Cuts/Box base parts - Base left.dxf
744.0 x 340.1
