croningp/NanoDiscovery/Experiments/Hardware/Platform box/Cuts/Box base parts - Left wall (Stego heater outline).dxf

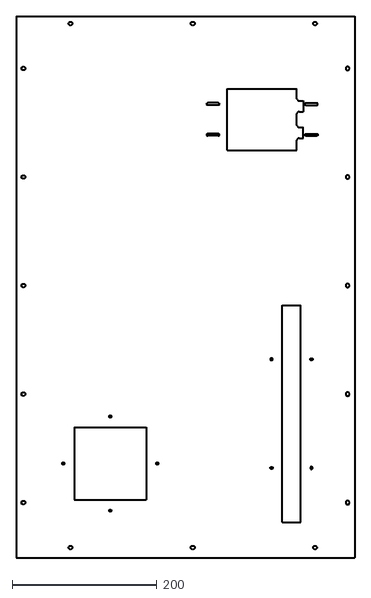
[picture p76: CAD file, 2022-08-24]
Experiments/Hardware/Platform box/Cuts/Box base parts - Left wall (Stego heater outline).dxf
468.0 x 748.0
