croningp/NanoDiscovery/Experiments/Hardware/Platform box/Cuts/Box base parts - Front.dxf

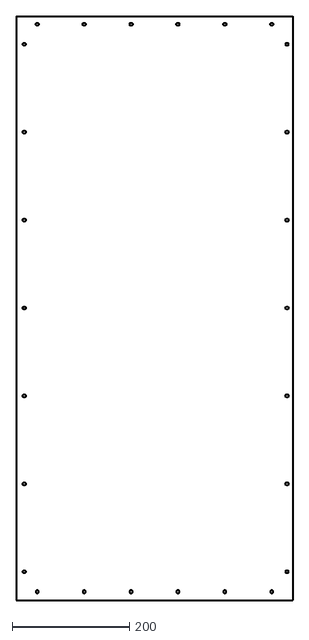
[picture p78: CAD file, 2022-08-24]
Experiments/Hardware/Platform box/Cuts/Box base parts - Front.dxf
472.0 x 996.0
