croningp/NanoDiscovery/Experiments/Algorithms/1-Optimization/1-Octahedron/Q_data.csv

2.283491611480712891e+00
2.281586751987037864e+00
2.279651513824631603e+00
2.277686199017055824e+00
2.275691109587871797e+00
2.273666547560639017e+00
2.271612814958920090e+00
2.269530213806275842e+00
2.267419046126265769e+00
2.265279613942453363e+00
2.263112219278397674e+00
2.260917164157659975e+00
2.258694750603801538e+00
2.256445280640384521e+00
2.254169056290967532e+00
2.251866379579113175e+00
2.249537552528382278e+00
2.247182877162336112e+00
2.244802655504534172e+00
2.242397189578539507e+00
2.239966781407912499e+00
2.237511733016212645e+00
2.235032346427002992e+00
2.232528923663843479e+00
2.230001766750295822e+00
2.227451177709919961e+00
2.224877458566278055e+00
2.222280911342929155e+00
2.219661838063437198e+00
2.217020540751360791e+00
2.214357321430262537e+00
2.211672482123701489e+00
2.208966324855240693e+00
2.206239151648440533e+00
2.203491264526861393e+00
2.200722965514064544e+00
2.197934556633611258e+00
2.195126576229960769e+00
2.192302250322500257e+00
2.189466511047788000e+00
2.186624317751502566e+00
2.183780629779318527e+00
2.180940406476915783e+00
2.178108607189971568e+00
2.175290191264161788e+00
2.172490118045165897e+00
2.169713346878658466e+00
2.166964837110319841e+00
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
