croningp/NanoDiscovery/Experiments/Algorithms/1-Optimization/1-Octahedron/Q_data_wavelength.csv

4.000000000000000222e-01
4.005505505505505548e-01
4.011011011011011429e-01
4.016516516516516755e-01
4.022022022022022081e-01
4.027527527527527962e-01
4.033033033033033288e-01
4.038538538538538614e-01
4.044044044044044495e-01
4.049549549549549821e-01
4.055055055055055147e-01
4.060560560560561028e-01
4.066066066066066353e-01
4.071571571571571679e-01
4.077077077077077560e-01
4.082582582582582886e-01
4.088088088088088212e-01
4.093593593593593538e-01
4.099099099099099419e-01
4.104604604604604745e-01
4.110110110110110071e-01
4.115615615615615952e-01
4.121121121121121278e-01
4.126626626626626604e-01
4.132132132132132485e-01
4.137637637637637811e-01
4.143143143143143137e-01
4.148648648648649018e-01
4.154154154154154344e-01
4.159659659659659670e-01
4.165165165165165551e-01
4.170670670670670876e-01
4.176176176176176202e-01
4.181681681681682083e-01
4.187187187187187409e-01
4.192692692692692735e-01
4.198198198198198616e-01
4.203703703703703942e-01
4.209209209209209268e-01
4.214714714714715149e-01
4.220220220220220475e-01
4.225725725725725801e-01
4.231231231231231682e-01
4.236736736736737008e-01
4.242242242242242334e-01
4.247747747747747660e-01
4.253253253253253541e-01
4.258758758758758867e-01
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
