croningp/NanoDiscovery/Experiments/Graph_Structure/reaction_graph.png

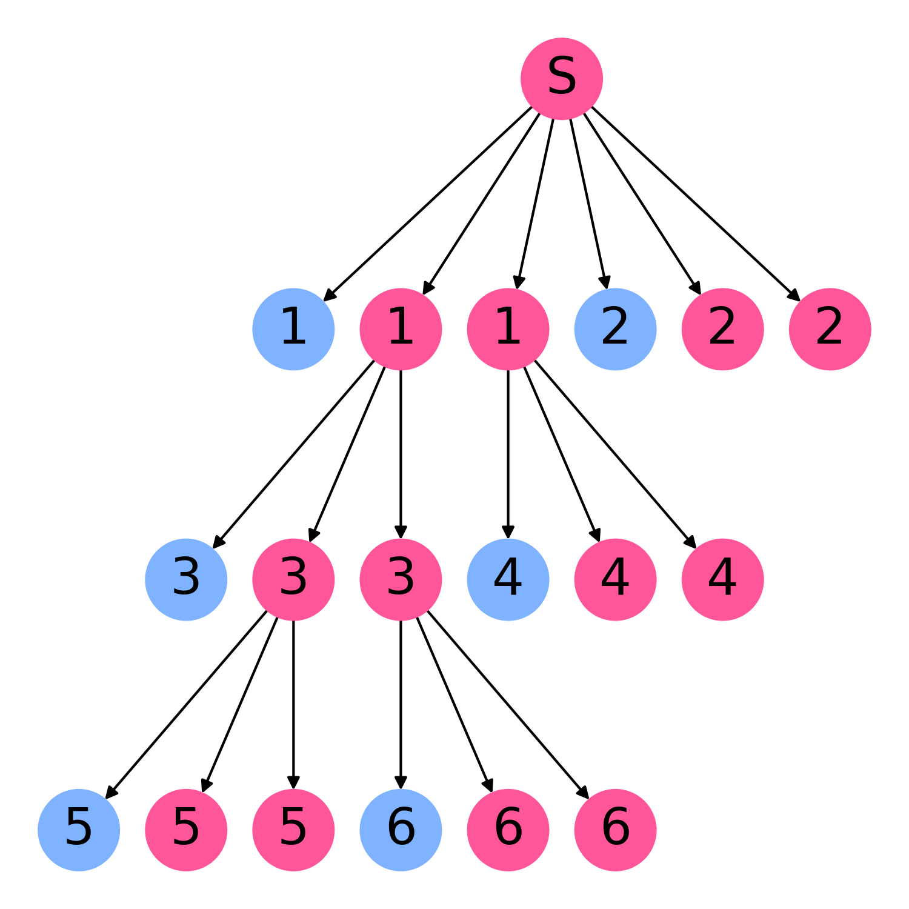
Experiments/Graph_Structure/reaction_graph.png
